ewyrick-mark-1/Chromatone/LPF.jpg

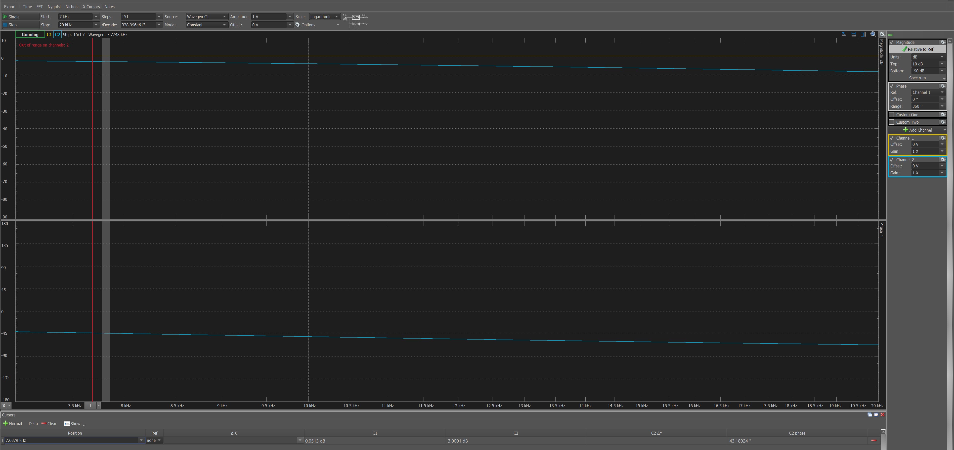
LPF.jpg
