ewyrick-mark-1/Chromatone/KiCad/4% possibilities/Proton Schematics/Debugger Schematic.jpg

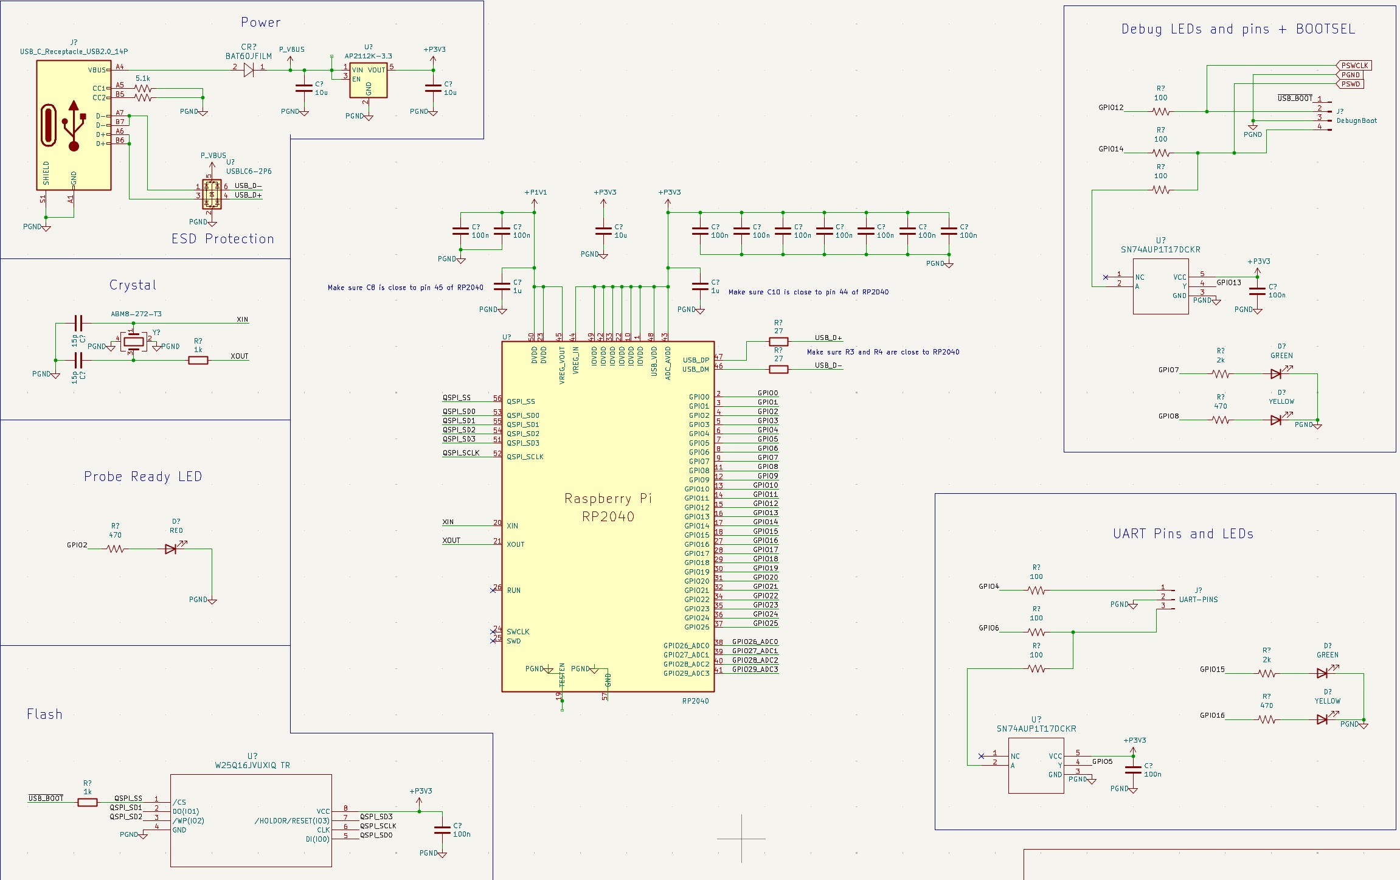
KiCad/4% possibilities/Proton Schematics/Debugger Schematic.jpg
