ewyrick-mark-1/Chromatone/KiCad/LTspice/Draft2.asc

C1: cap; 1nF
C2: cap; 1nF
C3: cap; 1nF
C4: cap; 1nF
C5: cap; 1nF
C6: cap; 10nF
R1: res; 18
R2: res; 11k
R3: res; 22k
R4: res; 8.2k
R5: res; 10k
R6: res; 10k
R7: res; 22k
R8: res; 1k
U1: UniversalOpAmp
U2: UniversalOpAmp
U3: UniversalOpAmp
V1: voltage; ""; AC 1
V2: voltage; ""; AC 1
V3: voltage; ""; AC 1
V4: voltage; ""; AC 1
Named nets: 0, BHPF, LPF, HPF, BLPF, BP_out
.ac dec 100 10 1Meg
