ewyrick-mark-1/Chromatone/KiCad/4% possibilities/Proton-KiCAD/Proton.kicad_pcb

## KiCad design KiCad/4% possibilities/Proton-KiCAD/Proton.kicad_pcb (2025-11-16)

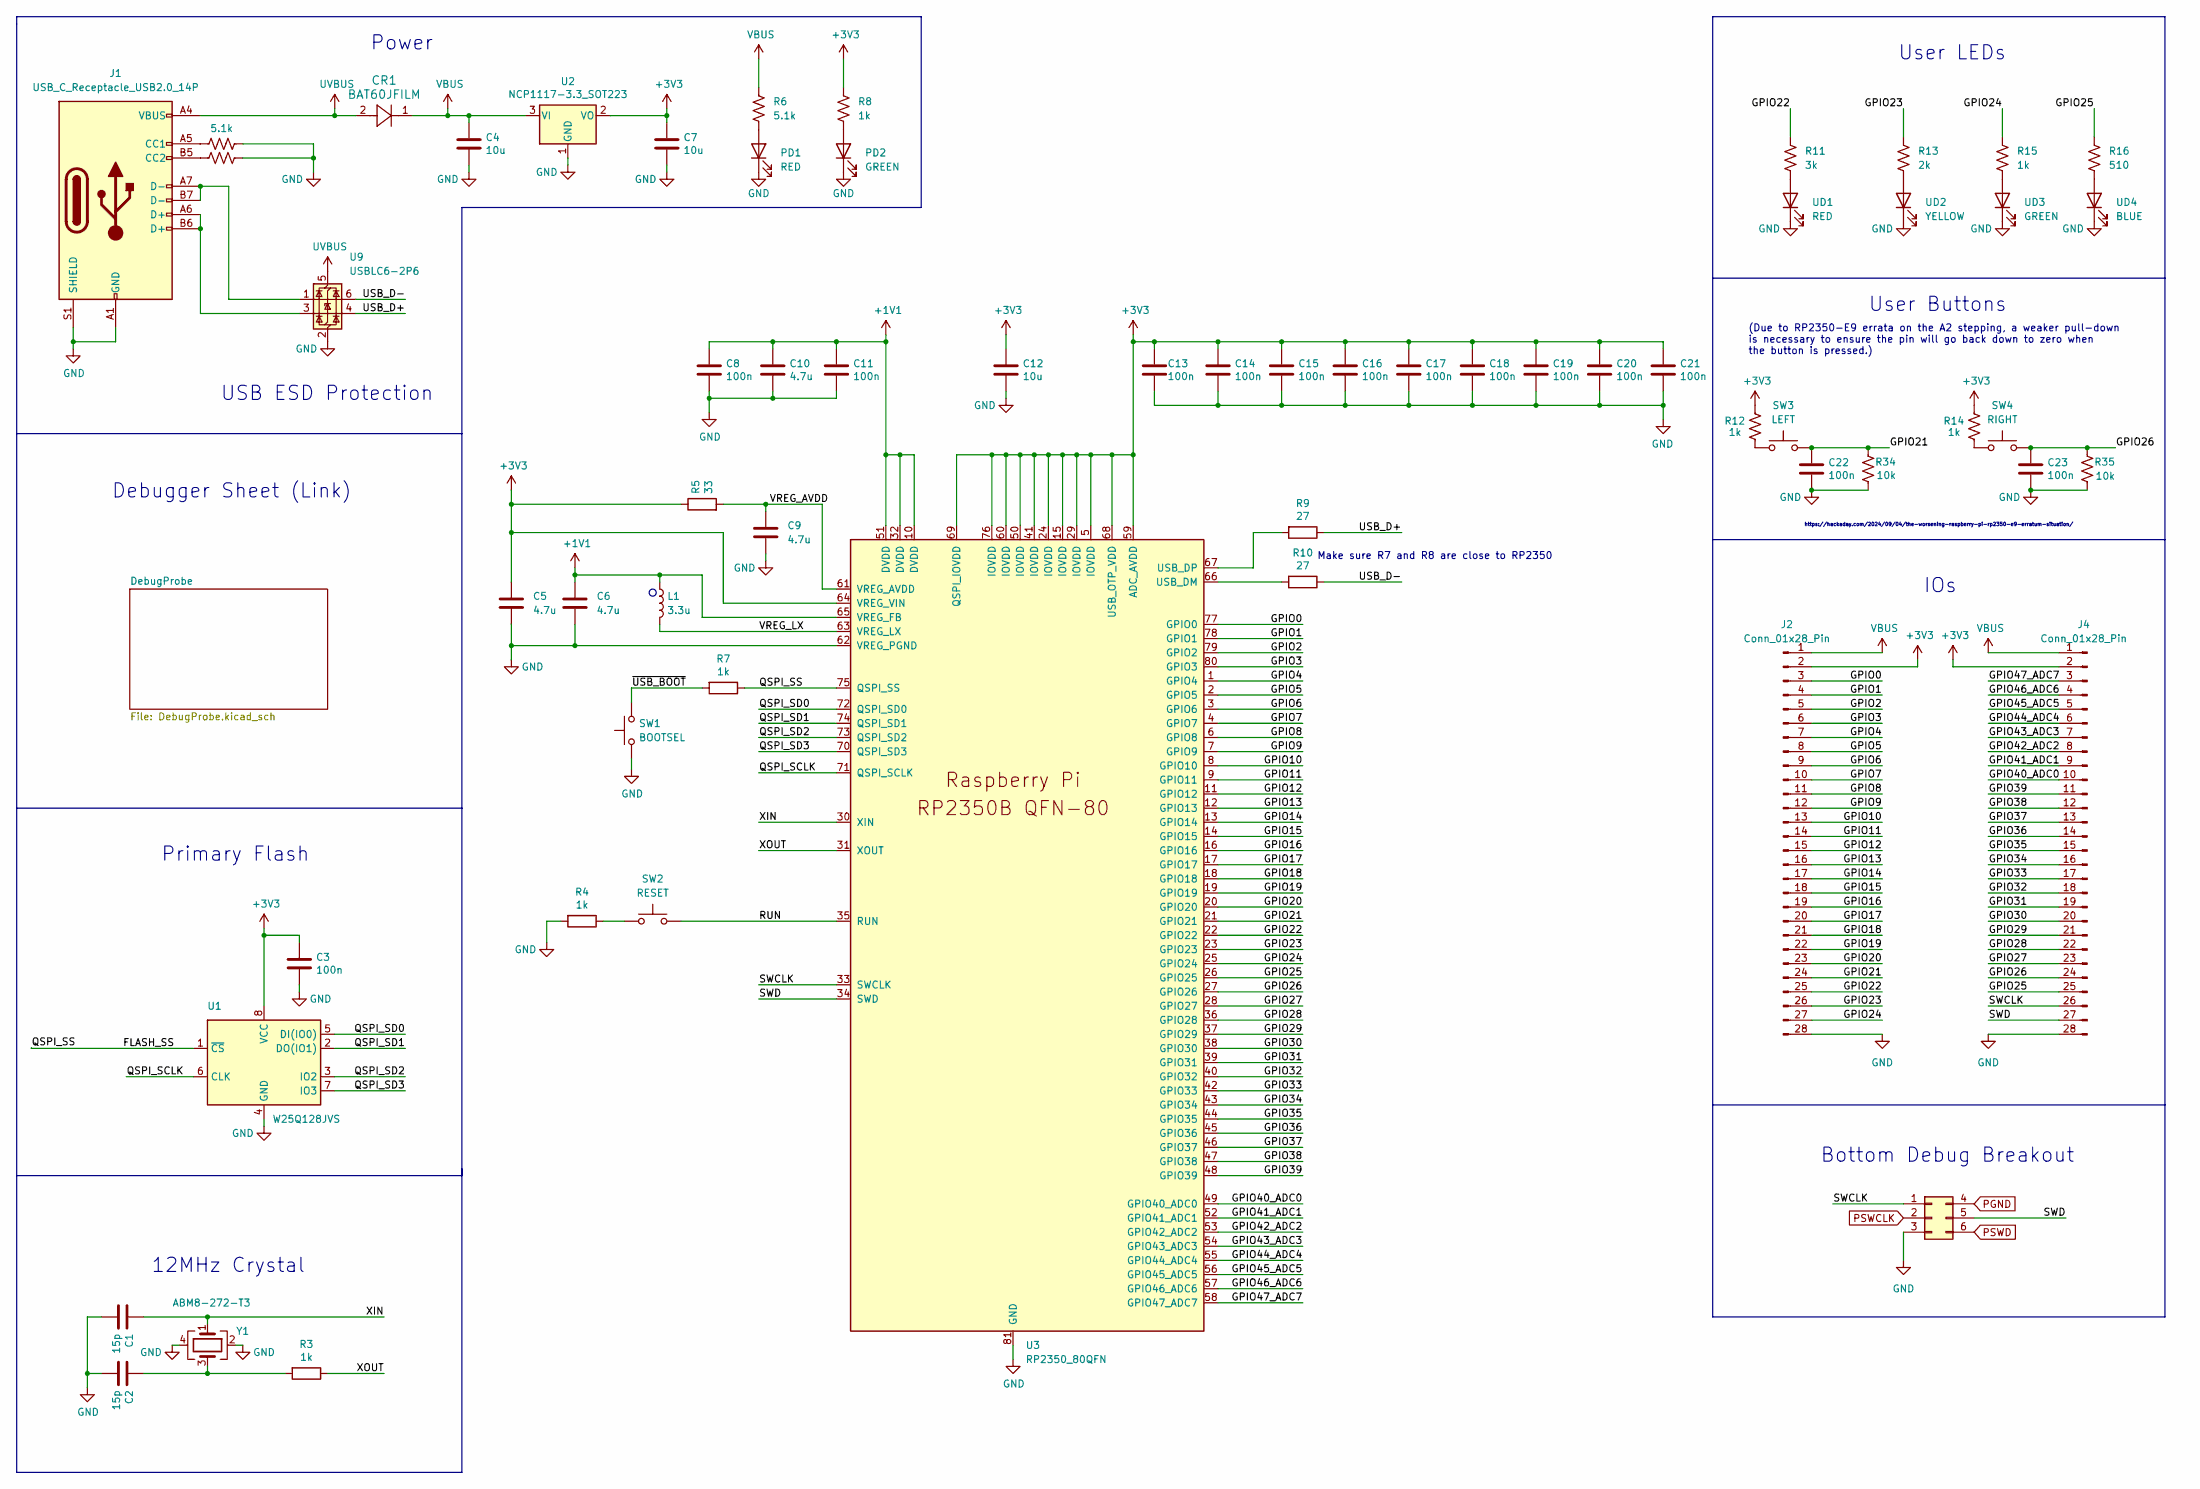
[picture p13: schematic Proton.kicad_sch, Purdue Proton]

Parts:
C1, C2: 15p; C_0402_1005Metric
C3, C8, C11, C13, C14, C15, C16, C17, C18, C19, C20, C21, C22, C23: 100n; C_0402_1005Metric
C4, C7, C12: 10u; C_0805_2012Metric
C5, C6: 4.7u; C_0402_1005Metric_small_pads
C9, C10: 4.7u; C_0402_1005Metric
CR1: BAT60JFILM; CR_60JFILM_STM
J1: USB_C_Receptacle_USB2.0_14P; USB_C_Receptacle_G-Switch_GT-USB-7010ASV
J2, J4: Conn_01x28_Pin; PinHeader_1x28_P2.54mm_Vertical
J6: Conn_02x03_Top_Bottom; PinSocket_2x03_P2.54mm_Vertical
L1: 3.3u; L_pol_2016
PD1: RED; LED_0805_2012Metric
PD2: GREEN; LED_0805_2012Metric
R1, R2, R6: 5.1k; R_0402_1005Metric
R3, R4, R7, R8, R12, R14, R15: 1k; R_0402_1005Metric
R5: 33; R_0402_1005Metric
R9, R10: 27; R_0402_1005Metric
R11: 3k; R_0402_1005Metric
R13: 2k; R_0402_1005Metric
R16: 510; R_0402_1005Metric
R34, R35: 10k; R_0402_1005Metric
SW1: BOOTSEL; SW_SPST_PTS647_Sx38
SW2: RESET; SW_SPST_PTS647_Sx38
SW3: LEFT; SW_SPST_PTS647_Sx38
SW4: RIGHT; SW_SPST_PTS647_Sx38
U1: W25Q128JVS; SOIC-8_5.23x5.23mm_P1.27mm
U2: NCP1117-3.3_SOT223; SOT-223-3_TabPin2
U3: RP2350_80QFN; RP2350-QFN-80-1EP_10x10_P0.4mm_EP3.4x3.4mm_ThermalVias
U9: USBLC6-2P6; SOT-666
UD1: RED; LED_0805_2012Metric
UD2: YELLOW; LED_0805_2012Metric
UD3: GREEN; LED_0805_2012Metric
UD4: BLUE; LED_0805_2012Metric
Y1: ABM8-272-T3; Crystal_SMD_3225-4Pin_3.2x2.5mm

Connections:
+1V1: C6.1, C8.1, C10.1, C11.1, L1.1, U3.10 (DVDD), U3.32 (DVDD), U3.51 (DVDD), U3.65 (VREG_FB)
+3V3: C3.1, C5.1, C7.1, C12.1, C13.1, C14.1, C15.1, C16.1, C17.1, C18.1, C19.1, C20.1, C21.1, J2.2, J4.2, R5.1, R8.1, R12.1, R14.1, U1.8 (VCC), U2.2 (VO), U3.5 (IOVDD), U3.15 (IOVDD), U3.24 (IOVDD), U3.29 (IOVDD), U3.41 (IOVDD), U3.50 (IOVDD), U3.59 (ADC_AVDD), U3.60 (IOVDD), U3.64 (VREG_VIN), U3.68 (USB_OTP_VDD), U3.69 (QSPI_IOVDD), U3.76 (IOVDD)
/FLASH_SS: R7.1, U1.1 (~CS), U3.75 (QSPI_SS)
/GPIO0: J2.3, U3.77 (GPIO0)
/GPIO1: J2.4, U3.78 (GPIO1)
/GPIO2: J2.5, U3.79 (GPIO2)
/GPIO3: J2.6, U3.80 (GPIO3)
/GPIO4: J2.7, U3.1 (GPIO4)
/GPIO5: J2.8, U3.2 (GPIO5)
/GPIO6: J2.9, U3.3 (GPIO6)
/GPIO7: J2.10, U3.4 (GPIO7)
/GPIO8: J2.11, U3.6 (GPIO8)
/GPIO9: J2.12, U3.7 (GPIO9)
/GPIO10: J2.13, U3.8 (GPIO10)
/GPIO11: J2.14, U3.9 (GPIO11)
/GPIO12: J2.15, U3.11 (GPIO12)
/GPIO13: J2.16, U3.12 (GPIO13)
/GPIO14: J2.17, U3.13 (GPIO14)
/GPIO15: J2.18, U3.14 (GPIO15)
/GPIO16: J2.19, U3.16 (GPIO16)
/GPIO17: J2.20, U3.17 (GPIO17)
/GPIO18: J2.21, U3.18 (GPIO18)
/GPIO19: J2.22, U3.19 (GPIO19)
/GPIO20: J2.23, U3.20 (GPIO20)
/GPIO21: C22.1, J2.24, R34.2, SW3.2, U3.21 (GPIO21)
/GPIO22: J2.25, R11.1, U3.22 (GPIO22)
/GPIO23: J2.26, R13.1, U3.23 (GPIO23)
/GPIO24: J2.27, R15.1, U3.25 (GPIO24)
/GPIO25: J4.25, R16.1, U3.26 (GPIO25)
/GPIO26: C23.1, J4.24, R35.2, SW4.2, U3.27 (GPIO26)
/GPIO27: J4.23, U3.28 (GPIO27)
/GPIO28: J4.22, U3.36 (GPIO28)
/GPIO29: J4.21, U3.37 (GPIO29)
/GPIO30: J4.20, U3.38 (GPIO30)
/GPIO31: J4.19, U3.39 (GPIO31)
/GPIO32: J4.18, U3.40 (GPIO32)
/GPIO33: J4.17, U3.42 (GPIO33)
/GPIO34: J4.16, U3.43 (GPIO34)
/GPIO35: J4.15, U3.44 (GPIO35)
/GPIO36: J4.14, U3.45 (GPIO36)
/GPIO37: J4.13, U3.46 (GPIO37)
/GPIO38: J4.12, U3.47 (GPIO38)
/GPIO39: J4.11, U3.48 (GPIO39)
/GPIO40_ADC0: J4.10, U3.49 (GPIO40_ADC0)
/GPIO41_ADC1: J4.9, U3.52 (GPIO41_ADC1)
/GPIO42_ADC2: J4.8, U3.53 (GPIO42_ADC2)
/GPIO43_ADC3: J4.7, U3.54 (GPIO43_ADC3)
/GPIO44_ADC4: J4.6, U3.55 (GPIO44_ADC4)
/GPIO45_ADC5: J4.5, U3.56 (GPIO45_ADC5)
/GPIO46_ADC6: J4.4, U3.57 (GPIO46_ADC6)
/GPIO47_ADC7: J4.3, U3.58 (GPIO47_ADC7)
/QSPI_SCLK: U1.6 (CLK), U3.71 (QSPI_SCLK)
/QSPI_SD0: U1.5 (DI(IO0)), U3.72 (QSPI_SD0)
/QSPI_SD1: U1.2 (DO(IO1)), U3.74 (QSPI_SD1)
/QSPI_SD2: U1.3 (IO2), U3.73 (QSPI_SD2)
/QSPI_SD3: U1.7 (IO3), U3.70 (QSPI_SD3)
/RUN: SW2.2, U3.35 (RUN)
/SWCLK: J4.26, J6.1, U3.33 (SWCLK)
/SWD: J4.27, J6.5, U3.34 (SWD)
/USB_D+: R9.1, U9.4 (I/O2)
/USB_D-: R10.1, U9.6 (I/O1)
/VREG_AVDD: C9.1, R5.2, U3.61 (VREG_AVDD)
/VREG_LX: L1.2, U3.63 (VREG_LX)
/XIN: C1.1, U3.30 (XIN), Y1.1
/XOUT: R3.1, U3.31 (XOUT)
/~USB_BOOT: R7.2, SW1.2
GND: C1.2, C2.2, C3.2, C4.2, C5.2, C6.2, C7.2, C8.2, C9.2, C10.2, C11.2, C12.2, C13.2, C14.2, C15.2, C16.2, C17.2, C18.2, C19.2, C20.2, C21.2, C22.2, C23.2, J1.A1 (GND), J1.A12 (GND), J1.B1 (GND), J1.B12 (GND), J1.S1 (SHIELD), J2.28, J4.28, J6.3, PD1.1 (K), PD2.1 (K), R1.2, R2.2, R4.2, R34.1, R35.1, SW1.1, U1.4 (GND), U2.1 (GND), U3.62 (VREG_PGND), U3.81 (GND), U9.2 (GND), UD1.1 (K), UD2.1 (K), UD3.1 (K), UD4.1 (K), Y1.2, Y1.4
unnamed: C2.1, R3.2, Y1.3
unnamed: J1.A5 (CC1), R1.1
unnamed: J1.B5 (CC2), R2.1
unnamed: J1.A6 (D+), J1.B6 (D+), U9.3 (I/O2)
unnamed: J1.A7 (D-), J1.B7 (D-), U9.1 (I/O1)
unnamed: PD1.2 (A), R6.2
unnamed: PD2.2 (A), R8.2
unnamed: R4.1, SW2.1
unnamed: R12.2, SW3.1
unnamed: R14.2, SW4.1
unnamed: R10.2, U3.66 (USB_DM)
unnamed: R9.2, U3.67 (USB_DP)
unnamed: R11.2, UD1.2 (A)
unnamed: R13.2, UD2.2 (A)
unnamed: R15.2, UD3.2 (A)
unnamed: R16.2, UD4.2 (A)
PGND: J6.4; also elsewhere on the board
PSWCLK: J6.2; also elsewhere on the board
PSWD: J6.6; also elsewhere on the board
UVBUS: CR1.2, J1.A4 (VBUS), J1.A9 (VBUS), J1.B4 (VBUS), J1.B9 (VBUS), U9.5 (VBUS)
VBUS: C4.1, CR1.1, J2.1, J4.1, R6.1, U2.3 (VI)

Notes on the sheet:
https://hackaday.com/2024/09/04/the-worsening-raspberry-pi-rp2350-e9-erratum-situation/
IOs
12MHz Crystal
Bottom Debug Breakout
Primary Flash
User LEDs
Make sure R7 and R8 are close to RP2350
Debugger Sheet (Link)
USB ESD Protection
User Buttons
Power
(Due to RP2350-E9 errata on the A2 stepping, a weaker pull-down is necessary to ensure the pin will go back down to zero when the button is pressed.)

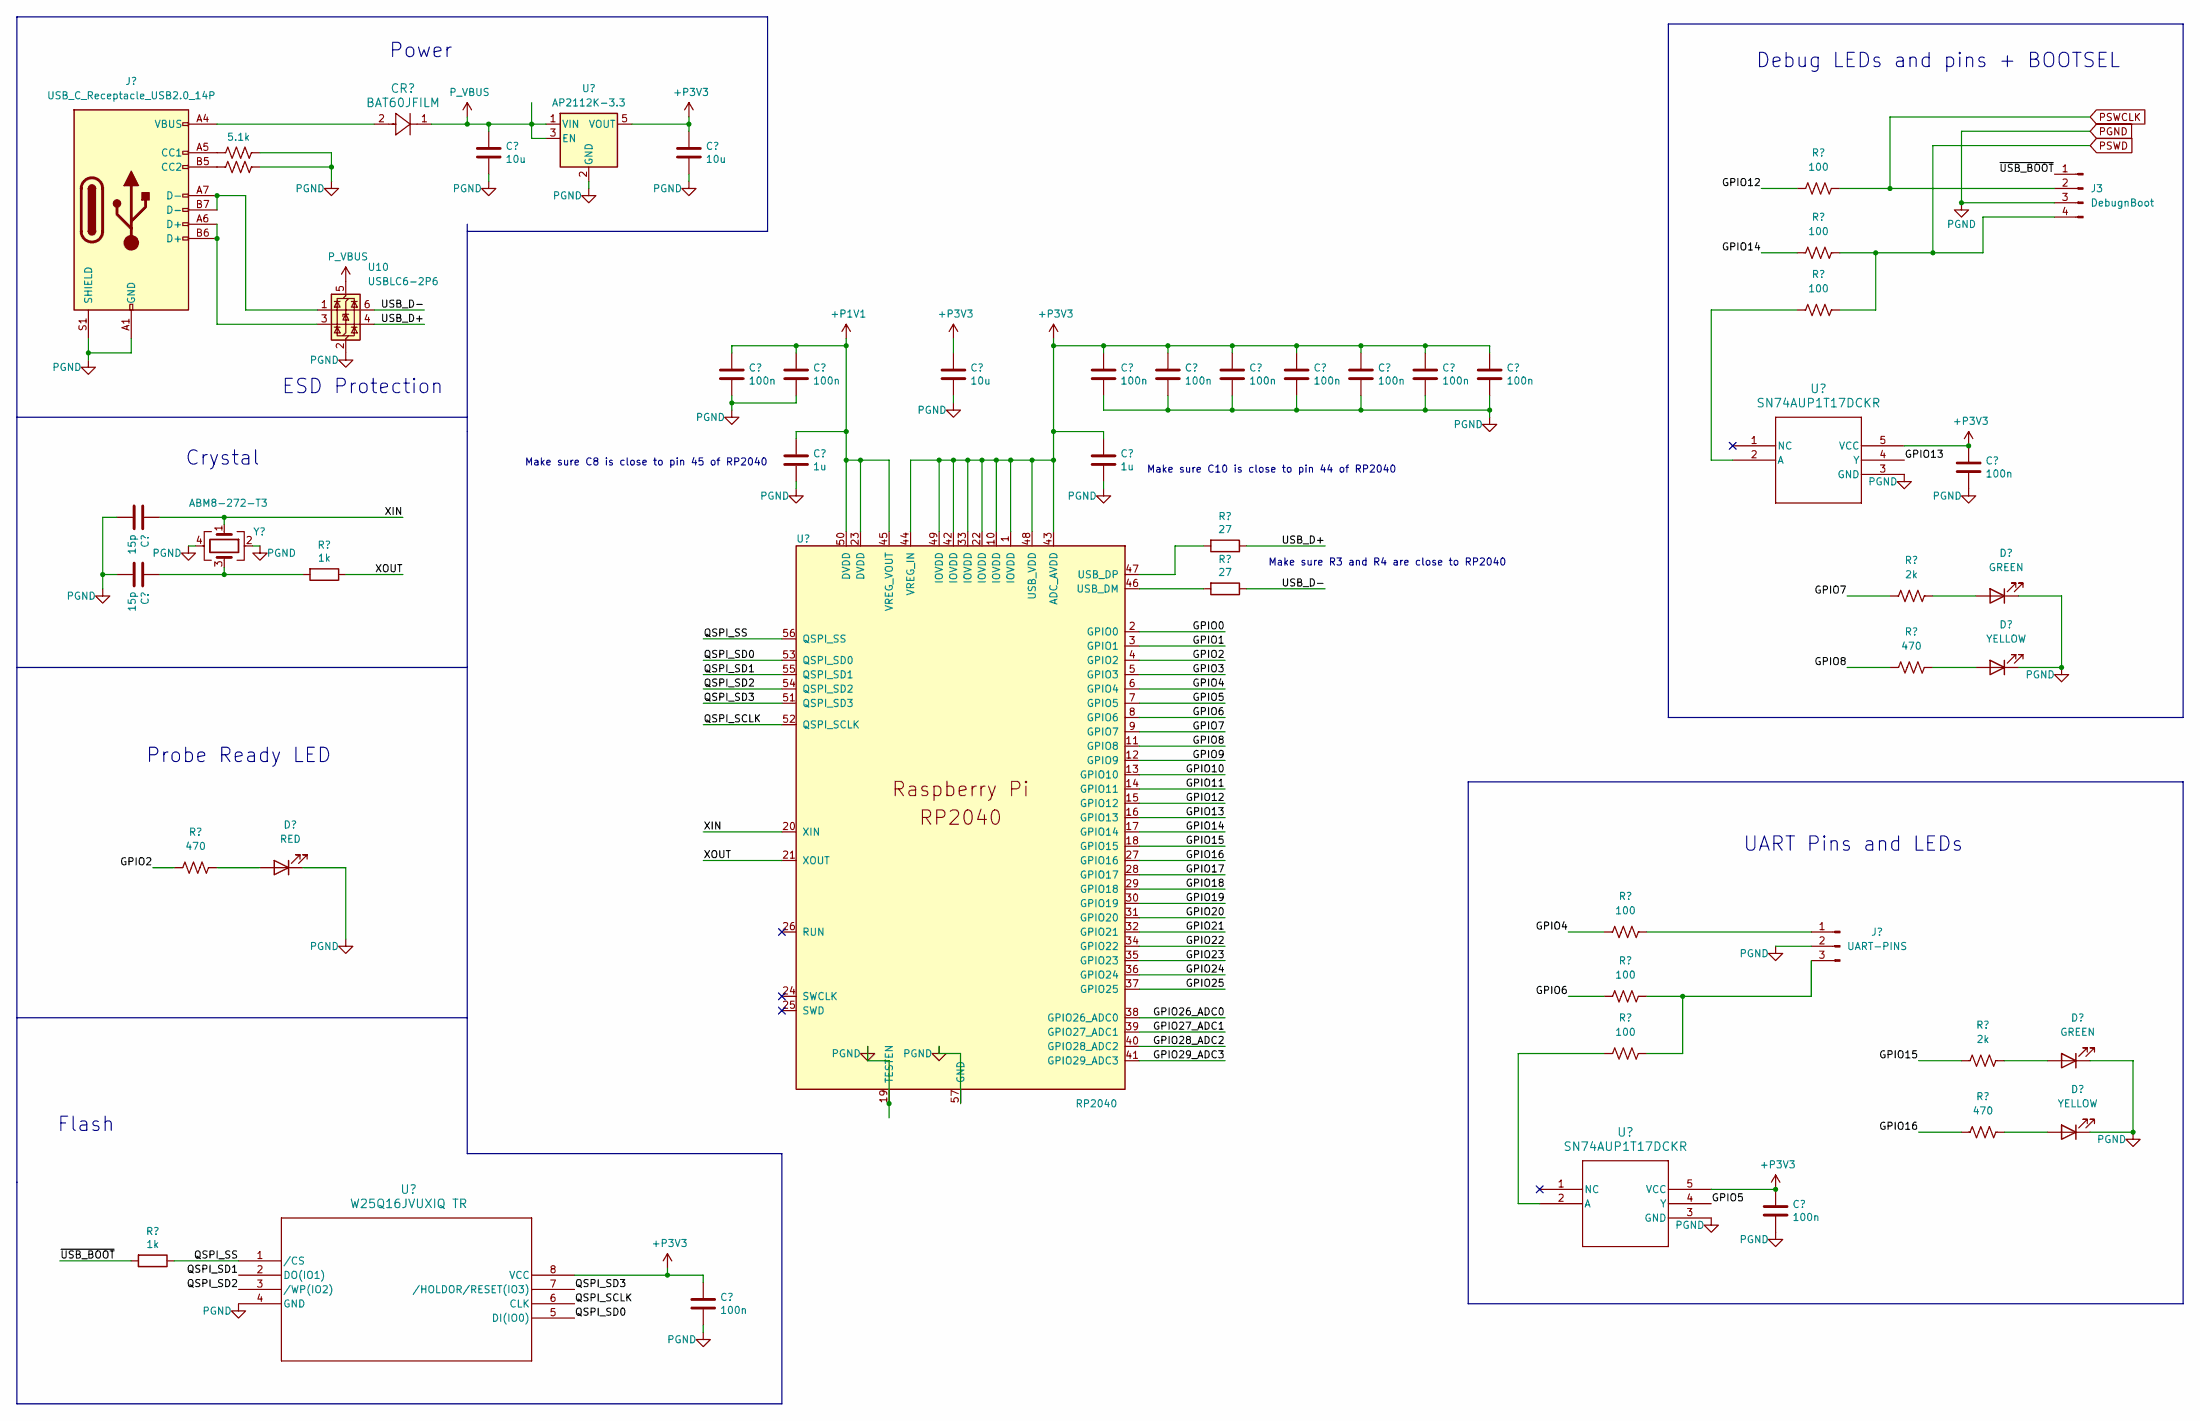
[picture p14: schematic DebugProbe.kicad_sch, Custom Debug Probe for DB-RP2350]

Parts:
C24, C25: 15p; C_0402_1005Metric
C26: 10u; C_0805_2012Metric
C27, C32: 10u; C_0603_1608Metric
C28, C29, C30, C33, C35, C36, C37, C38, C39, C40, C41, C42: 100n; C_0402_1005Metric
C31, C34: 1u; C_0402_1005Metric
CR2: BAT60JFILM; CR_60JFILM_STM
D1: RED; D_0402_1005Metric
D2, D4: GREEN; D_0402_1005Metric
D3, D5: YELLOW; D_0402_1005Metric
J3: DebugnBoot; PinHeader_1x04_P2.54mm_Vertical
J5: USB_C_Receptacle_USB2.0_14P; USB_C_Receptacle_G-Switch_GT-USB-7010ASV
J7: UART-PINS; PinHeader_1x03_P2.54mm_Vertical
R17, R20: 1k; R_0402_1005Metric
R18, R19: 5.1k; R_0402_1005Metric
R21, R22: 27; R_0402_1005Metric
R23, R31, R33: 470; R_0402_1005Metric
R24, R25, R26, R27, R28, R29: 100; R_0402_1005Metric
R30, R32: 2k; R_0402_1005Metric
U4: W25Q16JVUXIQ TR; USON-8_UX_2x3x0p6_WIN
U5: AP2112K-3.3; SOT-23-5
U6: RP2040; RP2040-QFN-56
U7, U8: SN74AUP1T17DCKR; DCK5
U10: USBLC6-2P6; SOT-666
Y2: ABM8-272-T3; Crystal_SMD_3225-4Pin_3.2x2.5mm

Connections:
+P1V1: C28.1, C30.1, C31.1, U6.23 (DVDD), U6.45 (VREG_VOUT), U6.50 (DVDD)
+P3V3: C27.1, C29.1, C32.1, C33.1, C34.1, C35.1, C36.1, C37.1, C38.1, C39.1, C40.1, C41.1, C42.1, U4.8 (VCC), U5.5 (VOUT), U6.1 (IOVDD), U6.10 (IOVDD), U6.22 (IOVDD), U6.33 (IOVDD), U6.42 (IOVDD), U6.43 (ADC_AVDD), U6.44 (VREG_IN), U6.48 (USB_VDD), U6.49 (IOVDD), U7.5 (VCC), U8.5 (VCC)
/DebugProbe/GPIO0: U6.2 (GPIO0)
/DebugProbe/GPIO1: U6.3 (GPIO1)
/DebugProbe/GPIO2: R23.1, U6.4 (GPIO2)
/DebugProbe/GPIO3: U6.5 (GPIO3)
/DebugProbe/GPIO4: R24.1, U6.6 (GPIO4)
/DebugProbe/GPIO5: U6.7 (GPIO5), U7.4 (Y)
/DebugProbe/GPIO6: R25.1, U6.8 (GPIO6)
/DebugProbe/GPIO7: R30.1, U6.9 (GPIO7)
/DebugProbe/GPIO8: R31.1, U6.11 (GPIO8)
/DebugProbe/GPIO9: U6.12 (GPIO9)
/DebugProbe/GPIO10: U6.13 (GPIO10)
/DebugProbe/GPIO11: U6.14 (GPIO11)
/DebugProbe/GPIO12: R27.1, U6.15 (GPIO12)
/DebugProbe/GPIO13: U6.16 (GPIO13), U8.4 (Y)
/DebugProbe/GPIO14: R28.1, U6.17 (GPIO14)
/DebugProbe/GPIO15: R32.1, U6.18 (GPIO15)
/DebugProbe/GPIO16: R33.1, U6.27 (GPIO16)
/DebugProbe/GPIO17: U6.28 (GPIO17)
/DebugProbe/GPIO18: U6.29 (GPIO18)
/DebugProbe/GPIO19: U6.30 (GPIO19)
/DebugProbe/GPIO20: U6.31 (GPIO20)
/DebugProbe/GPIO21: U6.32 (GPIO21)
/DebugProbe/GPIO22: U6.34 (GPIO22)
/DebugProbe/GPIO23: U6.35 (GPIO23)
/DebugProbe/GPIO24: U6.36 (GPIO24)
/DebugProbe/GPIO25: U6.37 (GPIO25)
/DebugProbe/GPIO26_ADC0: U6.38 (GPIO26_ADC0)
/DebugProbe/GPIO27_ADC1: U6.39 (GPIO27_ADC1)
/DebugProbe/GPIO28_ADC2: U6.40 (GPIO28_ADC2)
/DebugProbe/GPIO29_ADC3: U6.41 (GPIO29_ADC3)
/DebugProbe/QSPI_SCLK: U4.6 (CLK), U6.52 (QSPI_SCLK)
/DebugProbe/QSPI_SD0: U4.5 (DI(IO0)), U6.53 (QSPI_SD0)
/DebugProbe/QSPI_SD1: U4.2 (DO(IO1)), U6.55 (QSPI_SD1)
/DebugProbe/QSPI_SD2: U4.3 (/WP(IO2)), U6.54 (QSPI_SD2)
/DebugProbe/QSPI_SD3: U4.7 (/HOLDOR/RESET(IO3)), U6.51 (QSPI_SD3)
/DebugProbe/QSPI_SS: R17.1, U4.1 (/CS), U6.56 (QSPI_SS)
/DebugProbe/USB_D+: R21.1, U10.4 (I/O2)
/DebugProbe/USB_D-: R22.1, U10.6 (I/O1)
/DebugProbe/XIN: C24.1, U6.20 (XIN), Y2.1
/DebugProbe/XOUT: R20.1, U6.21 (XOUT)
/DebugProbe/~USB_BOOT: J3.1, R17.2
unnamed: C25.1, R20.2, Y2.3
unnamed: CR2.2, J5.A4 (VBUS), J5.A9 (VBUS), J5.B4 (VBUS), J5.B9 (VBUS)
unnamed: D1.2 (A), R23.2
unnamed: D2.2 (A), R30.2
unnamed: D3.2 (A), R31.2
unnamed: D4.2 (A), R32.2
unnamed: D5.2 (A), R33.2
unnamed: J5.A5 (CC1), R18.1
unnamed: J5.B5 (CC2), R19.1
unnamed: J5.A6 (D+), J5.B6 (D+), U10.3 (I/O2)
unnamed: J5.A7 (D-), J5.B7 (D-), U10.1 (I/O1)
unnamed: J7.1, R24.2
unnamed: J7.3, R25.2, R26.2
unnamed: R22.2, U6.46 (USB_DM)
unnamed: R21.2, U6.47 (USB_DP)
unnamed: R26.1, U7.2 (A)
unnamed: R29.1, U8.2 (A)
PGND: C24.2, C25.2, C26.2, C27.2, C28.2, C29.2, C30.2, C31.2, C32.2, C33.2, C34.2, C35.2, C36.2, C37.2, C38.2, C39.2, C40.2, C41.2, C42.2, D1.1 (K), D2.1 (K), D3.1 (K), D4.1 (K), D5.1 (K), J3.3, J5.A1 (GND), J5.A12 (GND), J5.B1 (GND), J5.B12 (GND), J5.S1 (SHIELD), J7.2, R18.2, R19.2, U4.4 (GND), U5.2 (GND), U6.19 (TESTEN), U6.57 (GND), U7.3 (GND), U8.3 (GND), U10.2 (GND), Y2.2, Y2.4; also elsewhere on the board
PSWCLK: J3.2, R27.2; also elsewhere on the board
PSWD: J3.4, R28.2, R29.2; also elsewhere on the board
P_VBUS: C26.1, CR2.1, U5.1 (VIN), U5.3 (EN), U10.5 (VBUS)

Notes on the sheet:
ESD Protection
Probe Ready LED
Crystal
Power
Make sure C8 is close to pin 45 of RP2040
Make sure C10 is close to pin 44 of RP2040
UART Pins and LEDs
Debug LEDs and pins + BOOTSEL
Make sure R3 and R4 are close to RP2040
Flash

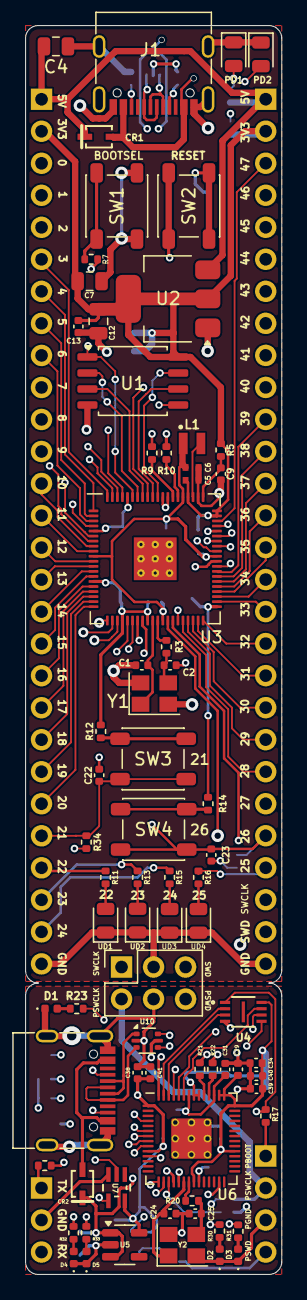
[picture p15: board Proton.kicad_pcb from above]

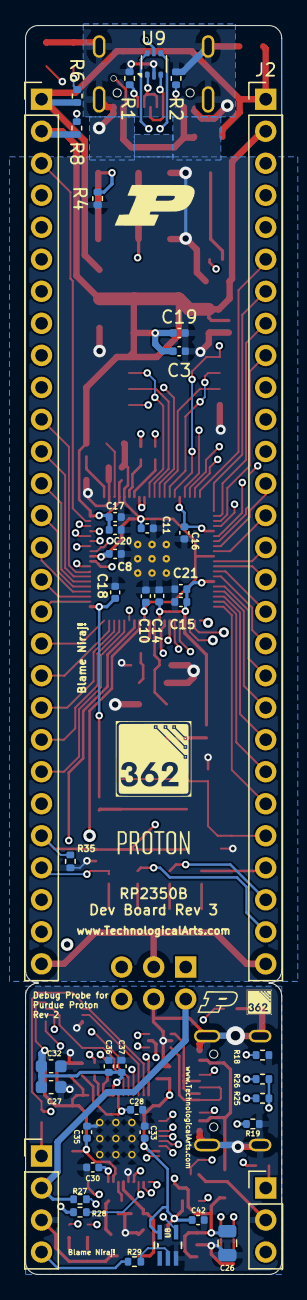
[picture p16: board Proton.kicad_pcb from below]

Board: 4 copper layers, 20.3 x 99.1 mm, 114 parts (41 on the bottom side), 130 nets.
